CedarGroveStudios/AD9833_ADSR_FeatherWing/photos/ADSR wave gen Dpot_bb.png

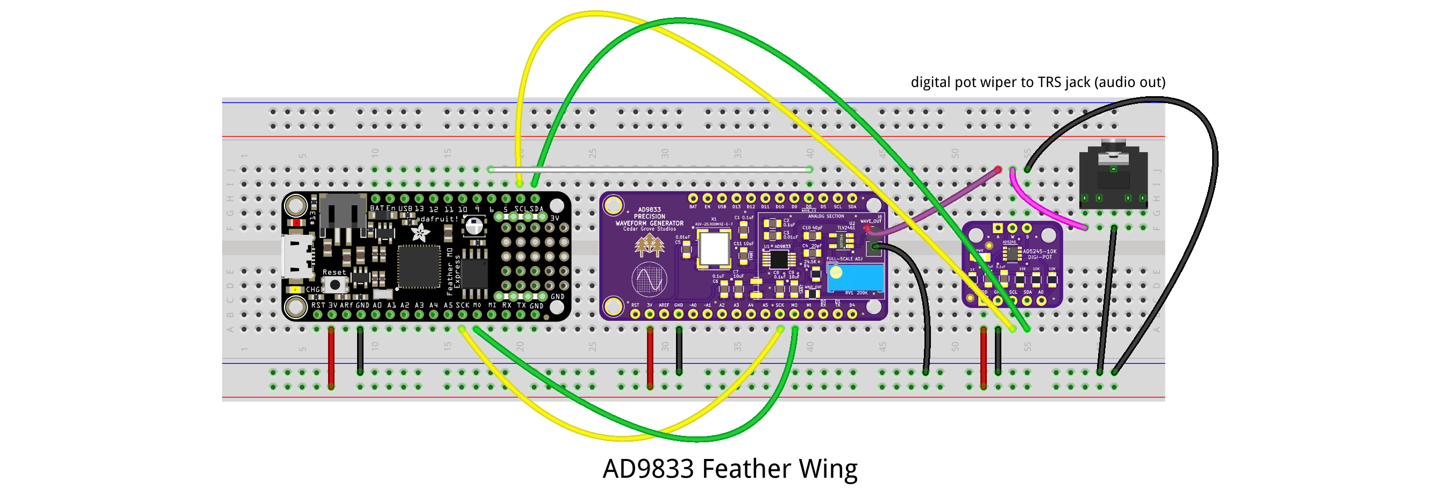
photos/ADSR wave gen Dpot_bb.png
