CedarGroveStudios/AD9833_ADSR_FeatherWing/photos/DSC05887anno.jpg

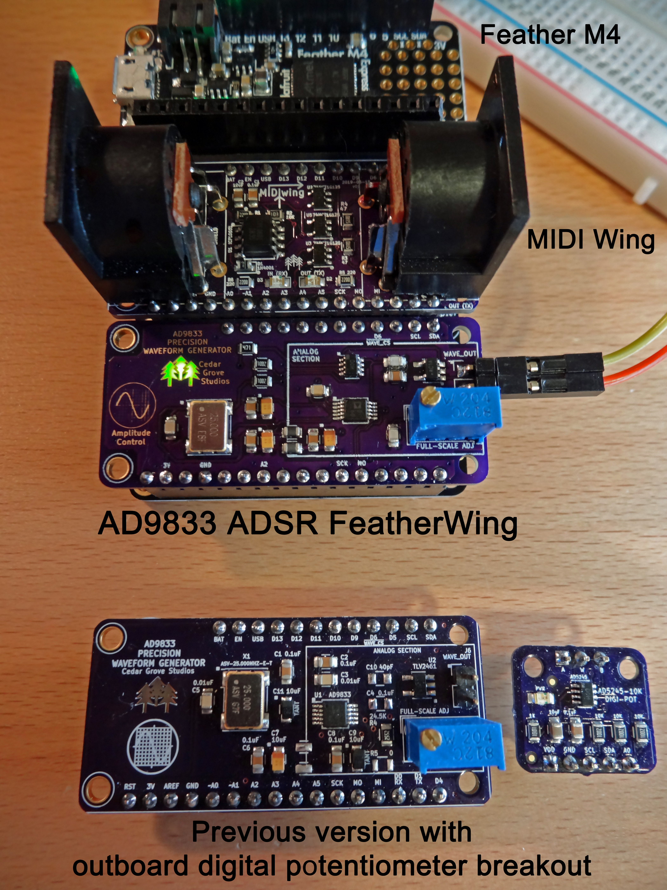
photos/DSC05887anno.jpg
