CedarGroveStudios/AD9833_ADSR_FeatherWing/photos/DSC05890combo.jpg

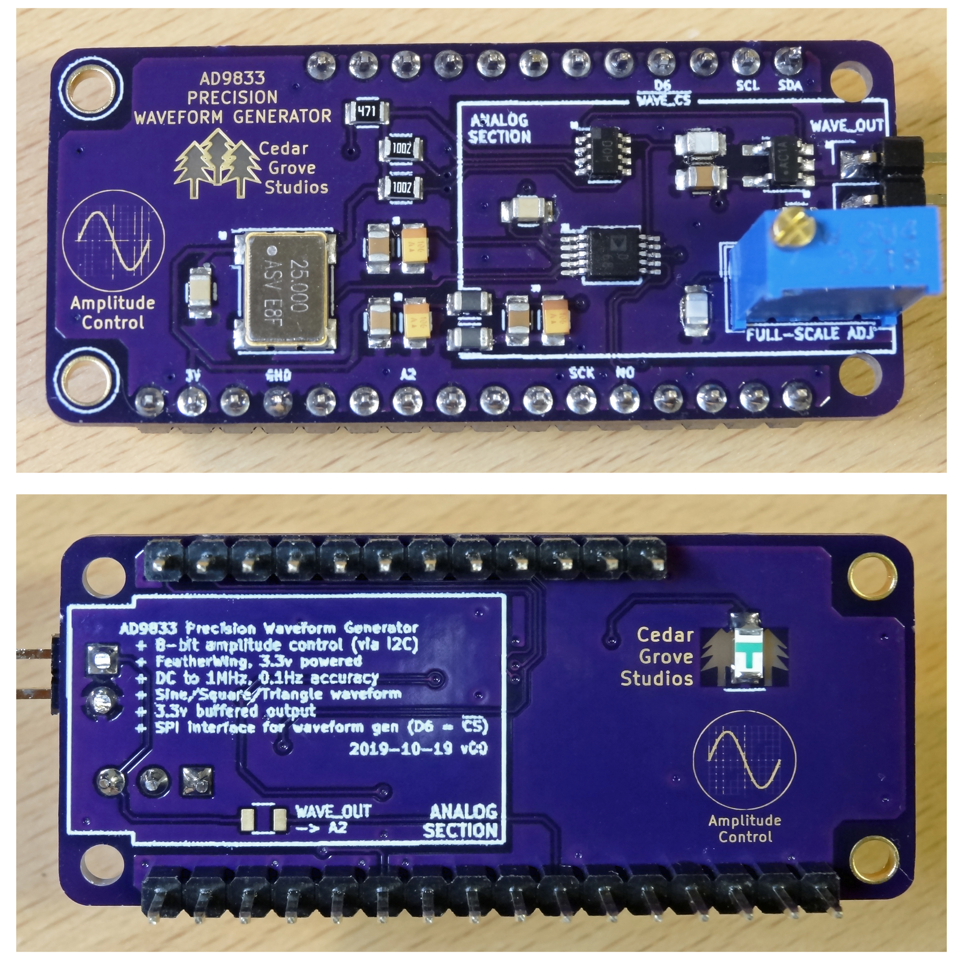
photos/DSC05890combo.jpg
