CedarGroveStudios/AD9833_ADSR_FeatherWing/photos/DSC05890combo_wide.jpg

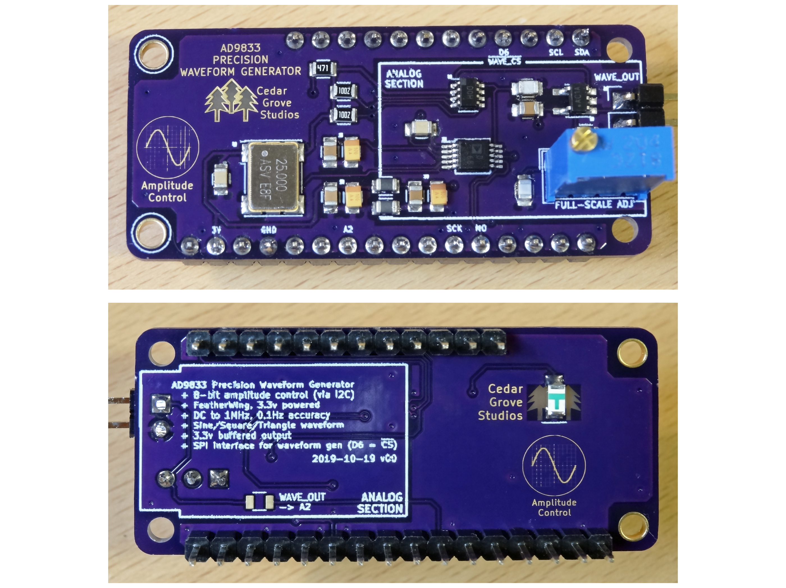
photos/DSC05890combo_wide.jpg
