CedarGroveStudios/AD9833_ADSR_FeatherWing/photos/DSC05901a.jpg

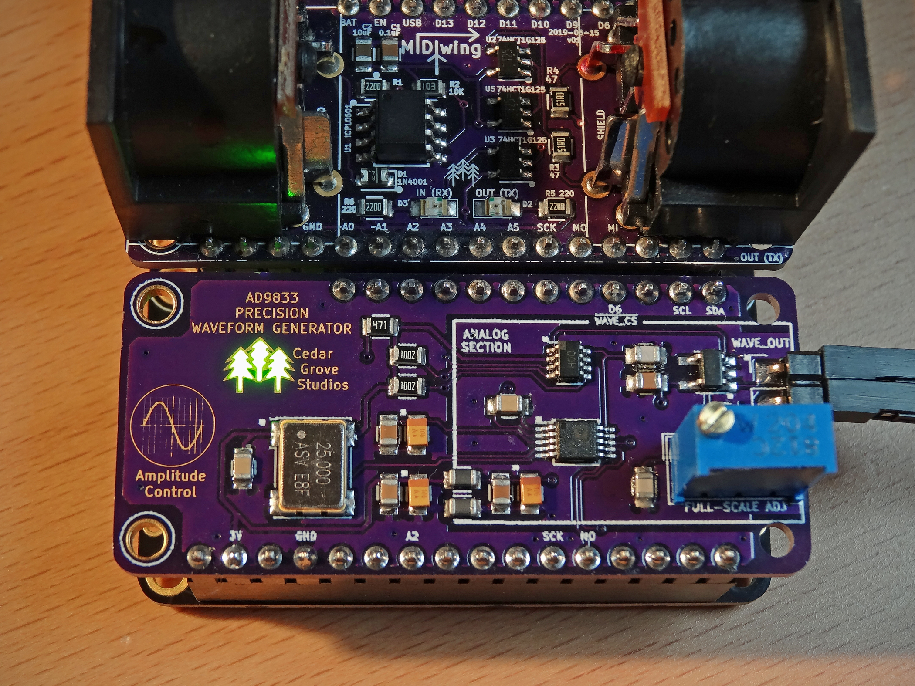
photos/DSC05901a.jpg
