CedarGroveStudios/AD9833_ADSR_FeatherWing/photos/DSC05901a_wide.jpg

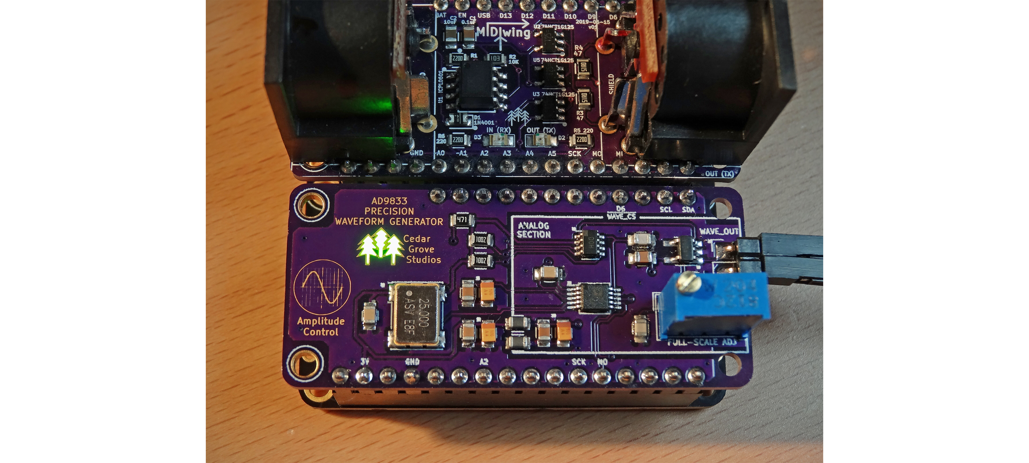
photos/DSC05901a_wide.jpg
