CedarGroveStudios/AD9833_ADSR_FeatherWing/photos/IMG_1215.JPG

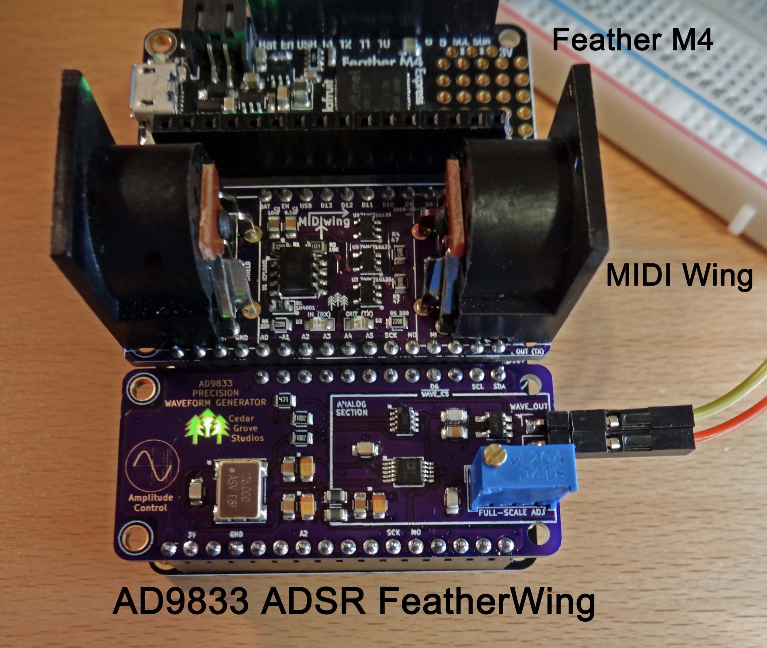
photos/IMG_1215.JPG
