CedarGroveStudios/AD9833_ADSR_FeatherWing/photos/smooth_ADSR_social.png

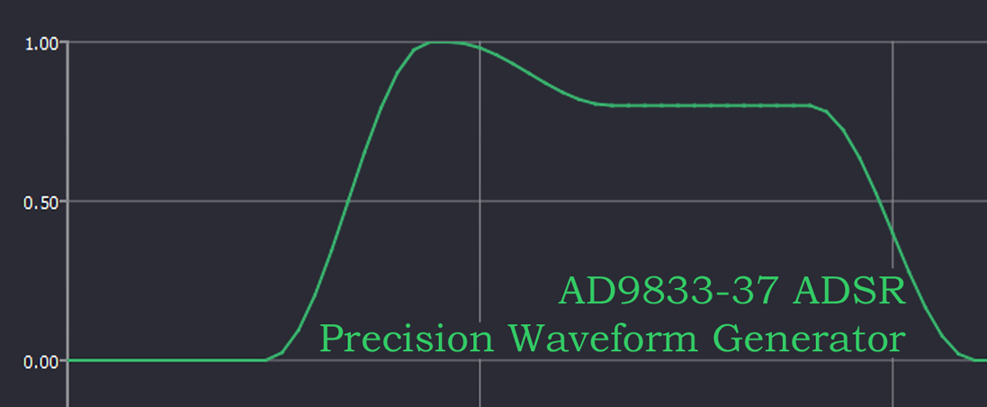
photos/smooth_ADSR_social.png
