CedarGroveStudios/AD9833_ADSR_FeatherWing/photos/Waveform_Gen_ADSR edge.png

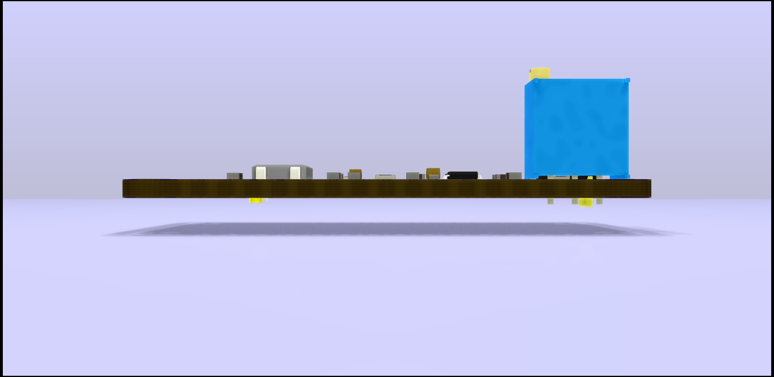
photos/Waveform_Gen_ADSR edge.png
