CedarGroveStudios/AD9833_ADSR_FeatherWing/photos/Waveform_Gen_ADSR.png

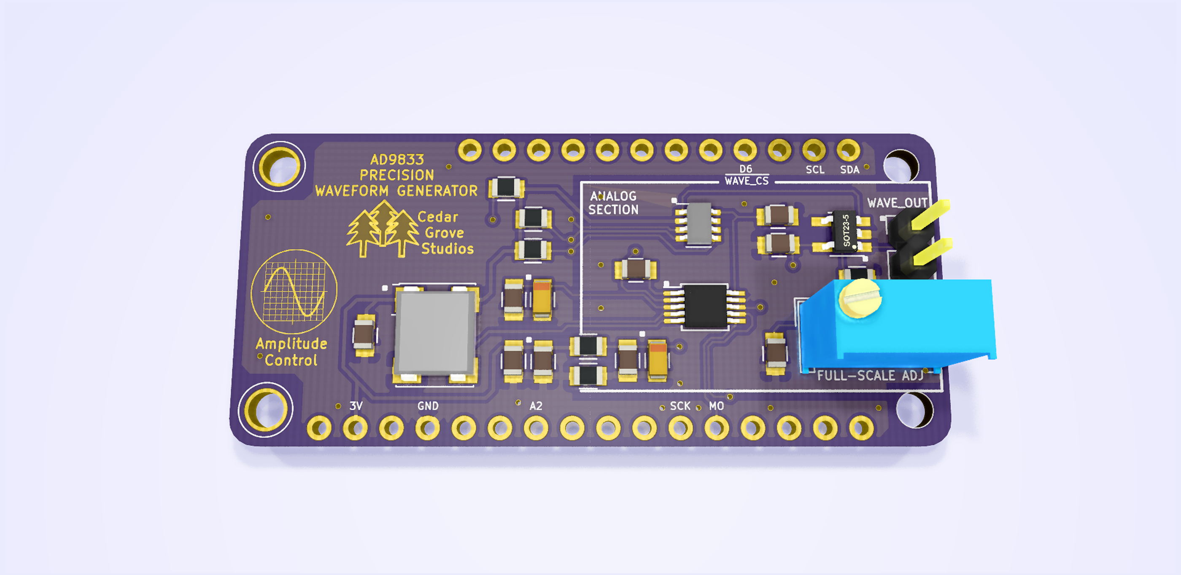
photos/Waveform_Gen_ADSR.png
