CedarGroveStudios/AD9833_ADSR_FeatherWing/photos/Waveform_Gen_ADSR_social.jpg

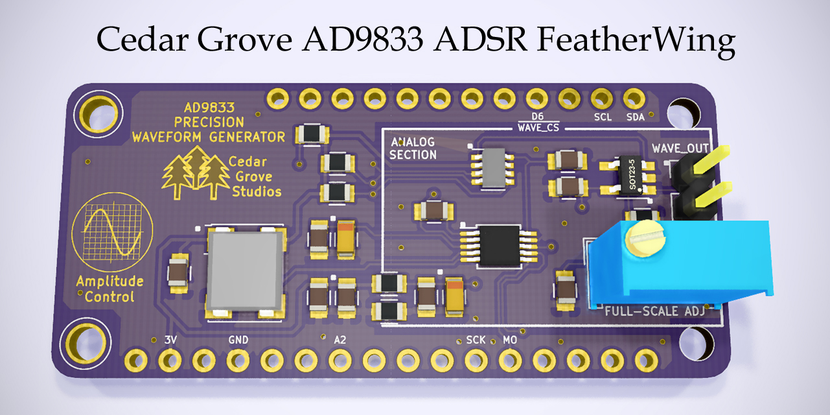
photos/Waveform_Gen_ADSR_social.jpg
