CedarGroveStudios/AD9833_ADSR_FeatherWing/photos/ADSR test oscope 2019-08-19.png

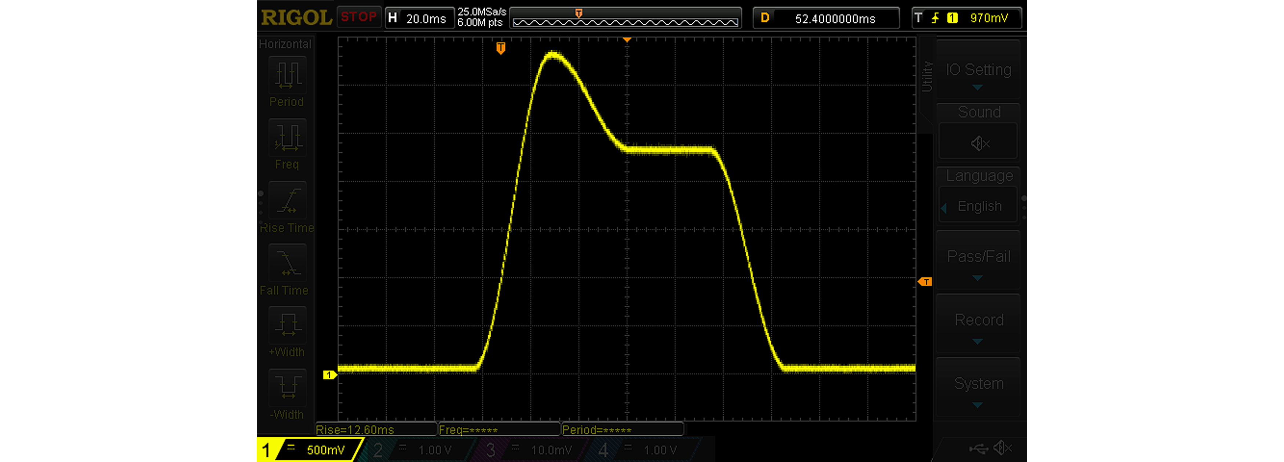
photos/ADSR test oscope 2019-08-19.png
